dossalab/Syma-s107-bluetooth-mod/firmware/src/state.rs

use crate::{
    ble::types::{ChargerState, Configuration, OcvMeasurement, PeriodicUpdate, QmaxUpdate, RaTableUpdate},
    types::{JoystickData, Request},
};
use defmt::{info, unwrap, warn};
use embassy_futures::select::{select4, Either4};
use embassy_sync::{
    blocking_mutex::raw::NoopRawMutex,
    watch::{Receiver, Sender, Watch},
};

pub type StateWatch<T> = Watch<NoopRawMutex, T, 8>;
pub type StateReceiver<'a, T> = Receiver<'a, NoopRawMutex, T, 8>;
pub type StateSender<'a, T> = Sender<'a, NoopRawMutex, T, 8>;

pub struct SystemState {
    pub charger_state: StateWatch<ChargerState>,
    pub soc: StateWatch<u8>,
    pub controller_connected: StateWatch<bool>,
    pub periodic_update: StateWatch<PeriodicUpdate>,
    pub controller_sample: StateWatch<JoystickData>,
    pub requests: StateWatch<Request>,
    pub controller_run_allowed: StateWatch<bool>,
    pub qmax_update: StateWatch<QmaxUpdate>,
    pub ocv_measurement: StateWatch<OcvMeasurement>,
    pub ratable_update: StateWatch<RaTableUpdate>,
    pub scan_state: StateWatch<bool>,
    pub config: StateWatch<Configuration>,
}

impl<'a> SystemState {
    pub fn new() -> Self {
        Self {
            charger_state: Watch::new(),
            soc: Watch::new(),
            controller_connected: Watch::new_with(false),
            periodic_update: Watch::new(),
            controller_sample: Watch::new(),
            requests: Watch::new(),
            controller_run_allowed: Watch::new_with(false),
            qmax_update: Watch::new_with(Default::default()),
            ocv_measurement: Watch::new_with(Default::default()),
            ratable_update: Watch::new_with(Default::default()),
            scan_state: Watch::new_with(false),
            config: Watch::new_with(Configuration::default()),
        }
    }
}

#[embassy_executor::task]
pub async fn run(state: &'static SystemState) {
    // Monitor the overall state of the system and provide a couple of
    // our own statuses as well
    info!("system state monitor running");

    let mut soc_receiver = unwrap!(state.soc.receiver());
    let mut controller_connected_receiver = unwrap!(state.controller_connected.receiver());
    let mut charger_state_receiver = unwrap!(state.charger_state.receiver());
    let mut requests_receiver = unwrap!(state.requests.receiver());
    let controller_run_allowed_sender = state.controller_run_allowed.sender();

    loop {
        controller_run_allowed_sender.send(matches!(
            (soc_receiver.try_get(), controller_connected_receiver.try_get(), charger_state_receiver.try_get()),
            (Some(soc), Some(true), Some(charger_state)) if soc > 5 && !charger_state.charging
        ));

        let s = select4(
            requests_receiver.changed(),
            soc_receiver.changed(),
            controller_connected_receiver.changed(),
            charger_state_receiver.changed(),
        )
        .await;

        match s {
            Either4::First(Request::Reboot) => {
                warn!("Reboot request is received");
                cortex_m::peripheral::SCB::sys_reset();
            }

            _ => {}
        }
    }
}
